TinyCircuits/TinyCircuits-TinyShield-Nordic_nRF8001_BLE-ASD2113/images/ASD2113-R-Tutorial-Image-03.jpg

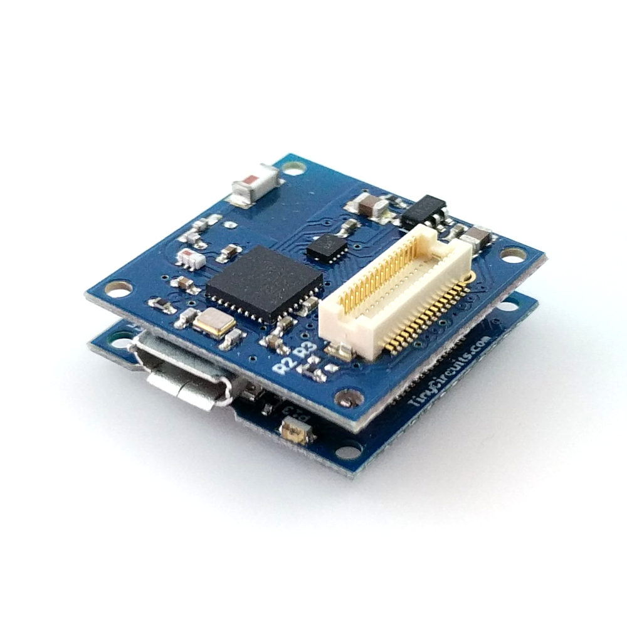
images/ASD2113-R-Tutorial-Image-03.jpg
